mikeblas/stoplight/stoplightd/stoplightd.cpp

#include <unistd.h>


#include <thread>
#include <chrono>

#include <daemonize/daemonizer.hpp>
#include <daemonize/syslog.hpp>
#include <daemonize/signals.hpp>

#include "modeinterface.h"

#include "modefactory.h"

#include "lights.h"
#include "buttons.h"

#include "stoplightd.h"

static const char* STOPLIGHT_CLIENT = "stoplight_remo";

static const char* chipname = "gpiochip0";

stoplightd::stoplightd(daemonize::logger& log)
   : daemon(log, "/run/stoplightd.pid", "/home/pi/"),
     lights(nullptr), buttons(nullptr), buzzer(nullptr),
     chip(nullptr), mode(nullptr),
     selectorMode(false), needRelease(false),
     runner(false),
     theThread(nullptr)
{
   log << log.critical << "stoplightd ctor" << std::endl;
   log << log.critical << "gpiod version: " << gpiod_version_string() << std::endl;
}

void stoplightd::SetupRunner()
{
   chip = gpiod_chip_open_by_name(chipname);

   if (chip == nullptr)
   {
      log << log.critical << "Open chip failed" << std::endl;
      throw 1;
   }

   lights = new Lights(STOPLIGHT_CLIENT, chip);
   buttons = new Buttons(STOPLIGHT_CLIENT, chip);
   buzzer = new SmartBuzzer(STOPLIGHT_CLIENT, chip);

   lights->AllOff();
   runner = true;
}


void stoplightd::DispatchMessages(ModeInterface* mode, Buttons& b2)
{
   // if this is a release decide what to do
   if (b2.GetVT() == 1)
   {
      buzzer->OneBeep();

      if (b2.GetAButton())
      {
         mode->OnAButtonPressed();
      }
      if (b2.GetBButton())
      {
         mode->OnBButtonPressed();
      }
      if (b2.GetCButton())
      {
         mode->OnCButtonPressed();
      }
      if (b2.GetDButton())
      {
         mode->OnDButtonPressed();
      }
   }
   else
   {
      if (b2.GetAButton())
      {
         mode->OnAButtonReleased();
      }
      if (b2.GetBButton())
      {
         mode->OnBButtonReleased();
      }

      if (b2.GetCButton())
      {
         mode->OnCButtonReleased();
      }
      if (b2.GetDButton())
      {
         mode->OnDButtonReleased();
      }
   }
}

void stoplightd::StartSelectorMode()
{

   mode = ModeFactory::FromModeNumber(0, *lights, *buzzer, log);
   selectorMode = true;

   log << log.critical << "starting selector mode thread" << std::endl;
   theThread = new std::thread(std::ref(*mode));
   log << log.critical << "selector mode thread started" << std::endl;
}


void stoplightd::run()
{
   log << log.critical << "stoplightd run function" << std::endl;

   SetupRunner();

   int ignores = 0;

   // get the lines, and get started!
   buttons->ReadLines();
   int lastVT = buttons->GetVT();

   // loop until we quit ...
   while (true)
   {

      buzzer->Advance();
      // log << log.critical << "Main loop advanced" << std::endl;
      lights->ToggleInd2();

      if (ignores > 0)
      {
         ignores--;
      }
      else
      {

         Buttons b2(STOPLIGHT_CLIENT, chip);
         b2.ReadLines();

         // if we have no mode, just see if any button pressed
         if (mode == nullptr)
         {
            if (b2.IsAnyButtonDown())
            {
               // enter selector mode
               log << log.critical << "starting selector mode from idle" << std::endl;

               StartSelectorMode();

               needRelease = true;

               // change states
               *buttons = b2;
               lastVT = b2.GetVT();
            }
         }
         else
         {
            // anything change since last time?
            if (b2 != *buttons || lastVT != b2.GetVT())
            {

               if (needRelease)
               {
                  if (b2.GetVT() == 1)
                  {
                     log << log.critical << "selector mode got release" << std::endl;
                     needRelease = false;
                  }
               }
               else
               {

                  // yes! print out the flags
                  buttons->LogState(log, "B1");
                  b2.LogState(log, "B2");

                  // ignore three loops to debounce
                  ignores = 3;

                  DispatchMessages(mode, b2);
               }

               // change states
               *buttons = b2;
               lastVT = b2.GetVT();
            }

            // did we quit?
            if (mode->IsQuitting())
            {
               log << log.critical << "Quitting! waiting for mode thread ..." << std::endl;

               mode->Shutdown();

               theThread->join();
               delete theThread;
               log << log.critical << "mode thread joined" << std::endl;

               // delete the mode
               delete mode;
               mode = nullptr;

               // if we were in selector mode, go to idle
               if (selectorMode)
               {
                  selectorMode = false;
                  log << log.critical << "returning to idle mode" << std::endl;
                  lights->AllOff();

                  buzzer->ThreeBeeps();
                  continue;
               }
               else
               {
                  // otherwise, it was a work mode and we return to selector mode
                  log << log.critical << "returning to selector mode" << std::endl;

                  // enter selector mode
                  mode = ModeFactory::FromModeNumber(0, *lights, *buzzer, log);
                  selectorMode = true;

                  log << log.critical << "starting selector mode thread" << std::endl;
                  theThread = new std::thread(std::ref(*mode));
                  log << log.critical << "selector mode thread started" << std::endl;

                  buzzer->TwoBeeps();
                  continue;
               }
            }

            // are we switching modes?
            int newMode = mode->NewMode();
            if (newMode != -1)
            {
               log << log.critical << "New mode selected: " << newMode << std::endl;
               mode->Shutdown();
               delete mode;

               mode = ModeFactory::FromModeNumber(newMode + 1, *lights, *buzzer, log);

               if (mode == nullptr)
               {

                  log << log.critical << "waiting for thread" << std::endl;

                  // bogus mode, go to sleep
                  theThread->join();
                  delete theThread;
                  theThread = nullptr;
                  log << log.critical << "idle mode" << std::endl;
                  lights->AllOff();

                  buzzer->ThreeBeeps();
               }
               else
               {

                  log << log.critical << "starting new mode thread" << std::endl;
                  theThread = new std::thread(std::ref(*mode));

                  buzzer->TwoBeeps();
               }

               selectorMode = false;
            }
         }
      }

      // sleep 50 ms between tests
      using namespace std::chrono_literals;
      std::this_thread::sleep_for(50ms);
   }
}
